digitaldex/piMeter_hardware/eagle/1.png

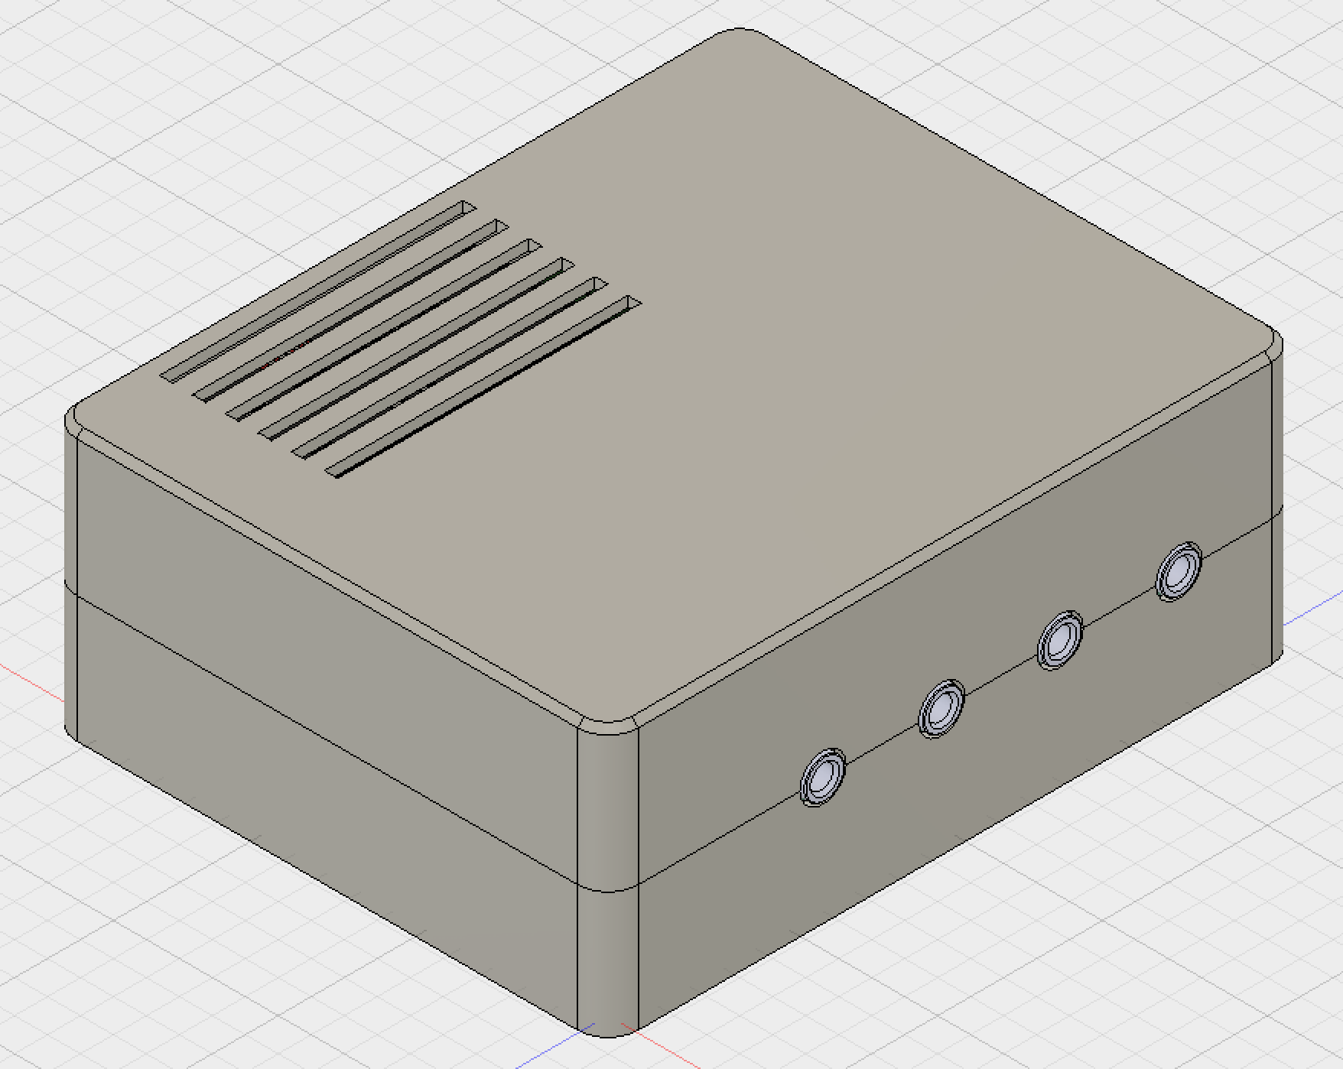
eagle/1.png
