digitaldex/piMeter_hardware/eagle/2.png

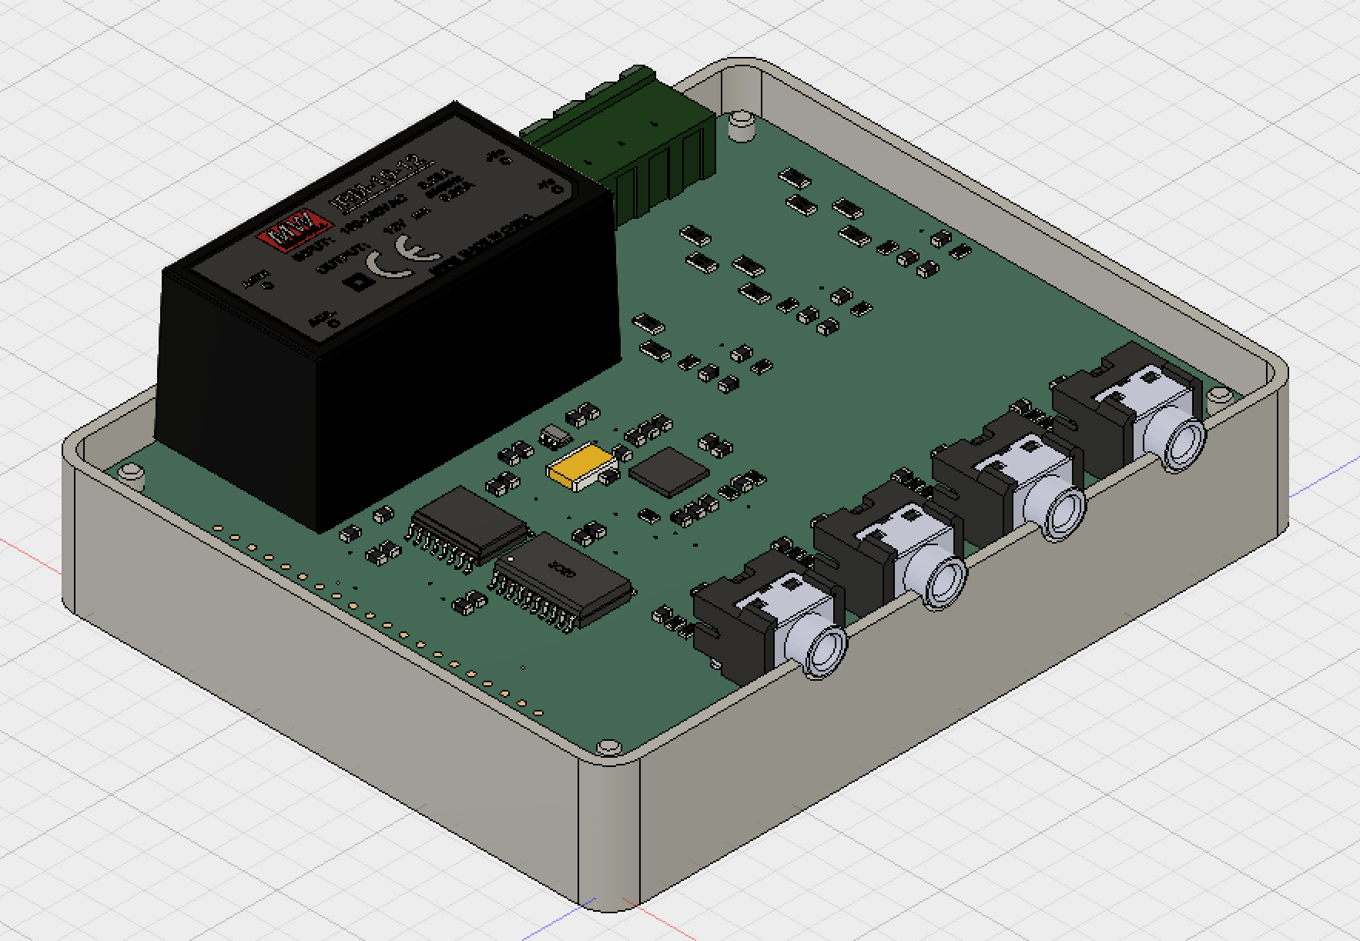
eagle/2.png
