digitaldex/piMeter_hardware/eagle/3.png

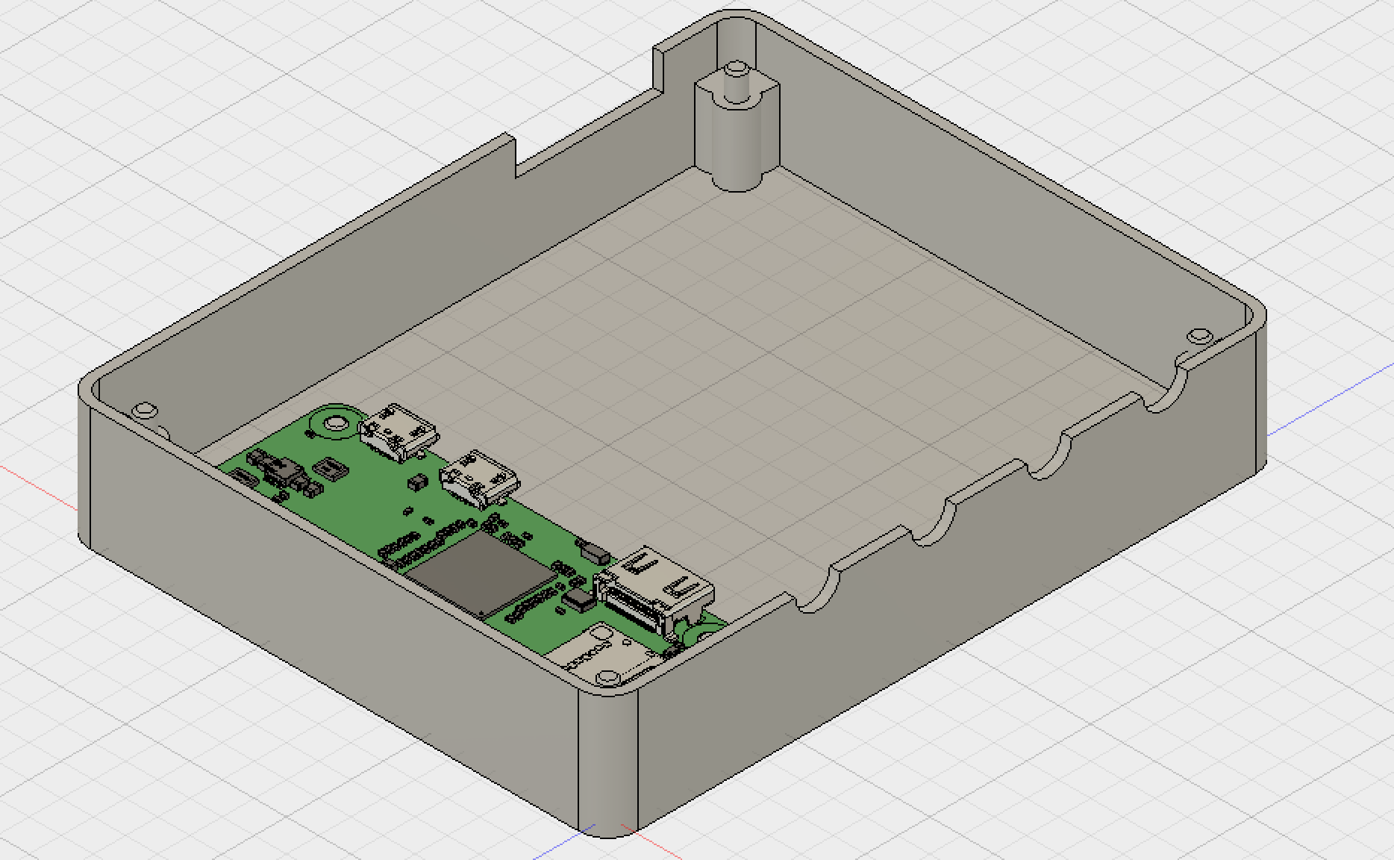
eagle/3.png
